matthieu-sgi/Internet-of-Plants/documentation/user_study/charts/plant_interaction_chart.png

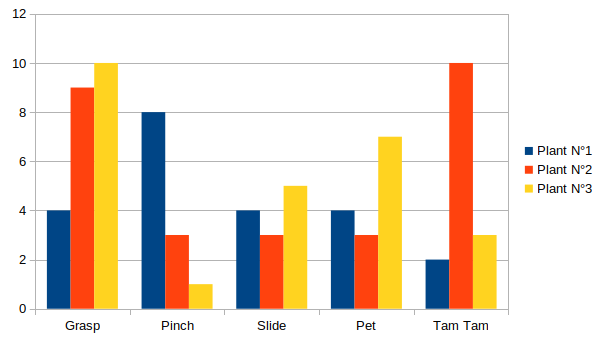
documentation/user_study/charts/plant_interaction_chart.png
