matthieu-sgi/Internet-of-Plants/documentation/user_study/media/IMG_20231115_154253.jpg

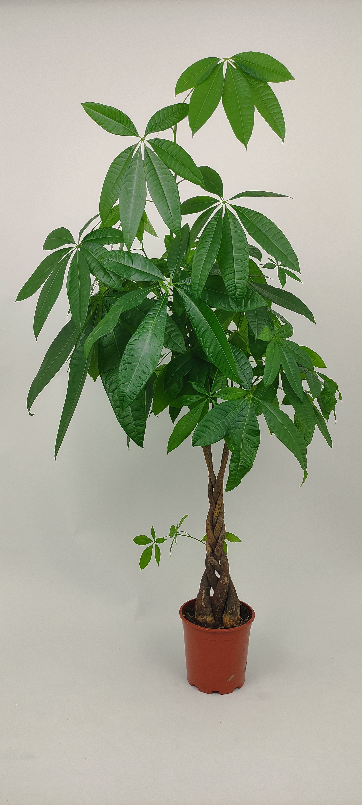
documentation/user_study/media/IMG_20231115_154253.jpg
