matthieu-sgi/Internet-of-Plants/documentation/user_study/media/IMG_20231115_154408.jpg

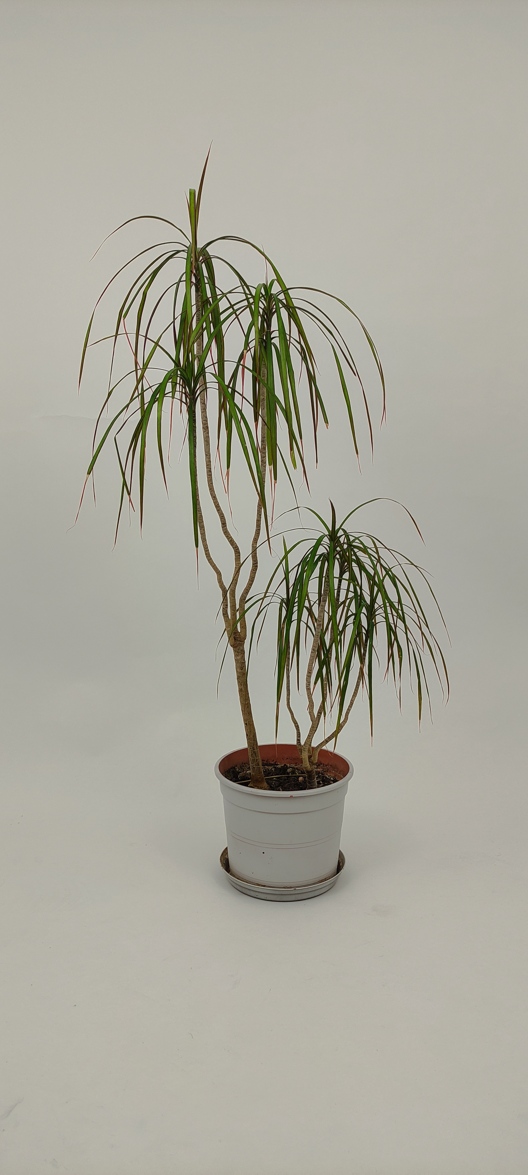
documentation/user_study/media/IMG_20231115_154408.jpg
