matthieu-sgi/Internet-of-Plants/documentation/user_study/media/IMG_20231115_155932.jpg

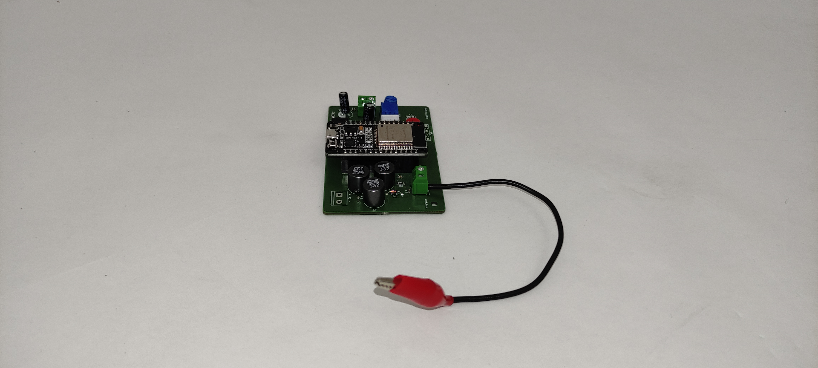
documentation/user_study/media/IMG_20231115_155932.jpg
