matthieu-sgi/Internet-of-Plants/documentation/user_study/media/IMG_20231115_160021.jpg

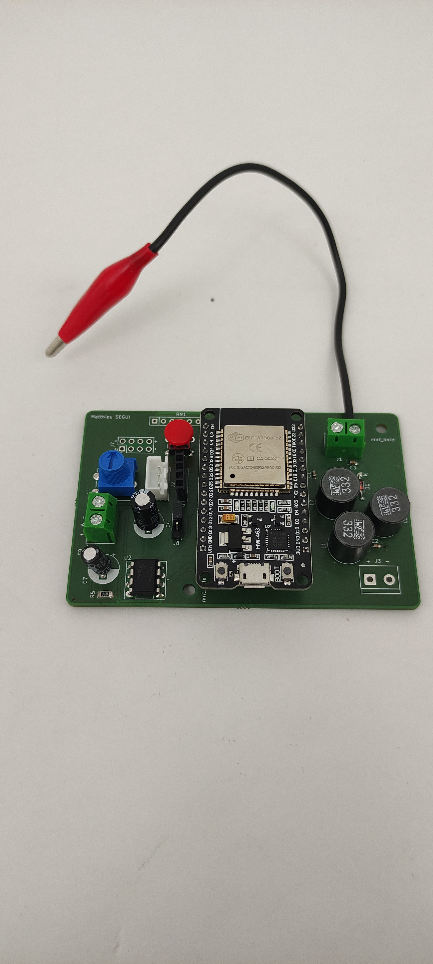
documentation/user_study/media/IMG_20231115_160021.jpg
