matthieu-sgi/Internet-of-Plants/documentation/user_study/media/raw/1699971025793.jpg

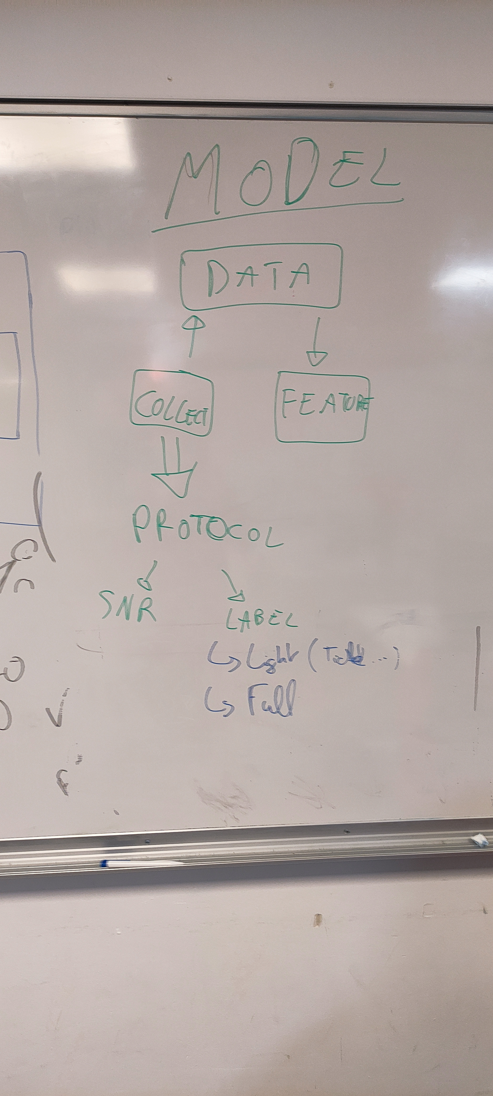
documentation/user_study/media/raw/1699971025793.jpg
