matthieu-sgi/Internet-of-Plants/documentation/user_study/media/raw/1699971025814.jpg

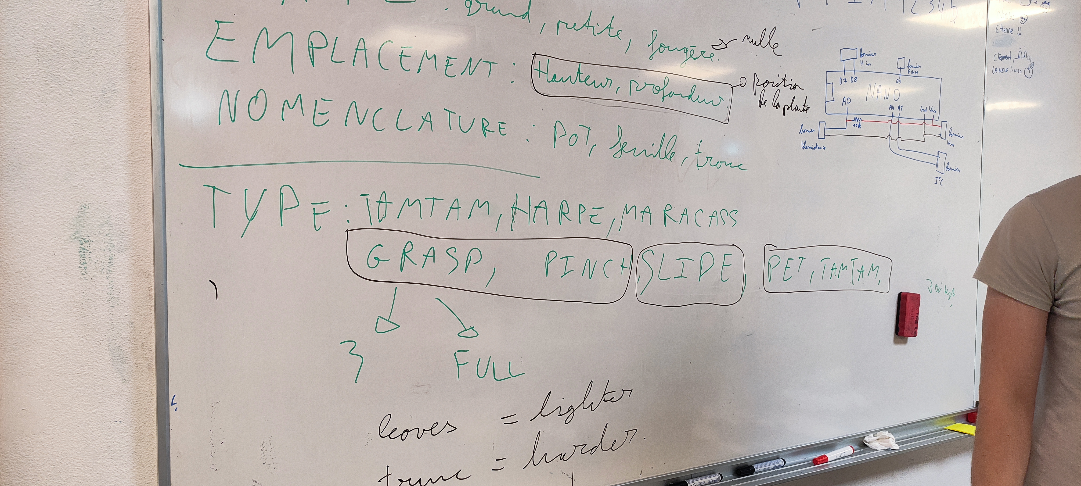
documentation/user_study/media/raw/1699971025814.jpg
