matthieu-sgi/Internet-of-Plants/documentation/user_study/user_study_plant_interaction/Images/iop_triangle.png

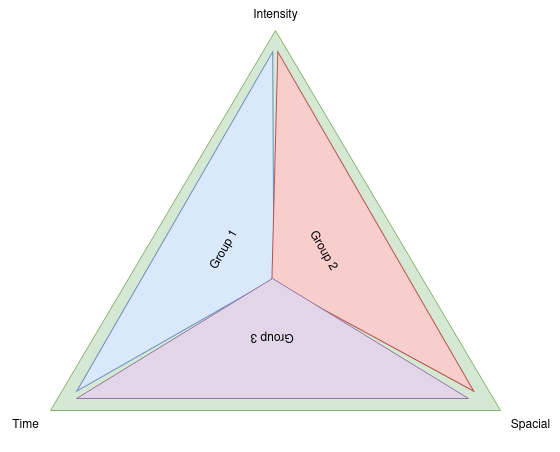
documentation/user_study/user_study_plant_interaction/Images/iop_triangle.png
