matthieu-sgi/Internet-of-Plants/media/3D_view_front.png

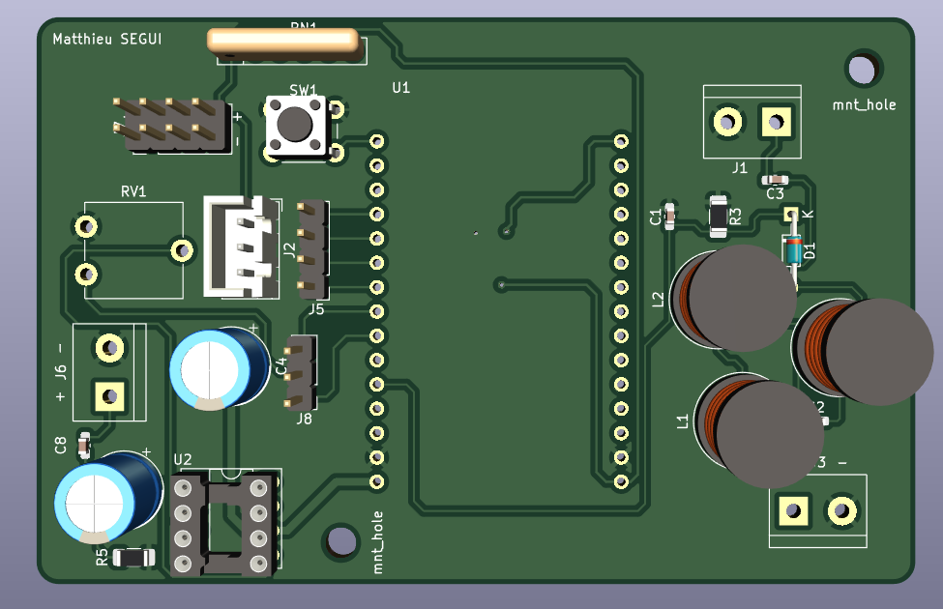
media/3D_view_front.png
