matthieu-sgi/Internet-of-Plants/media/3D_view_front_modif.png

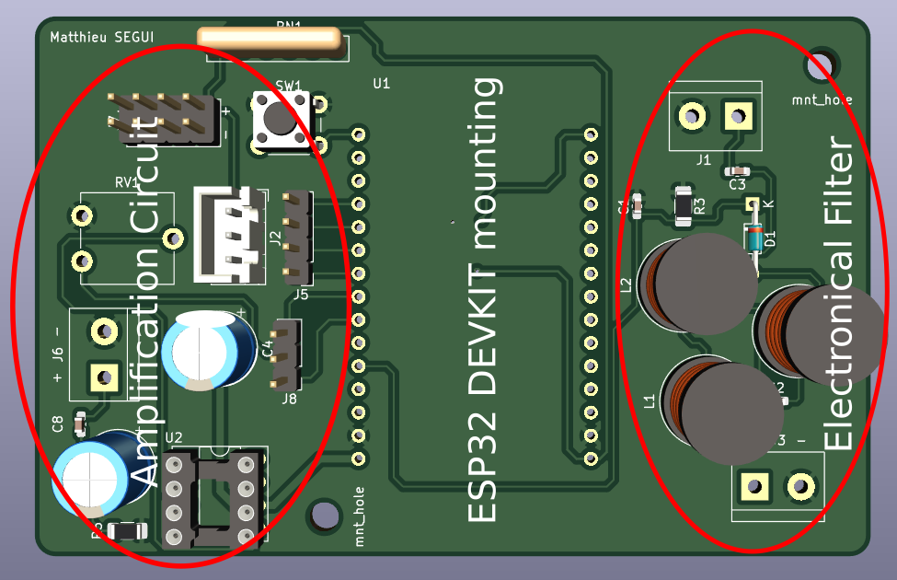
media/3D_view_front_modif.png
