matthieu-sgi/Internet-of-Plants/media/esp32_signal.jpg

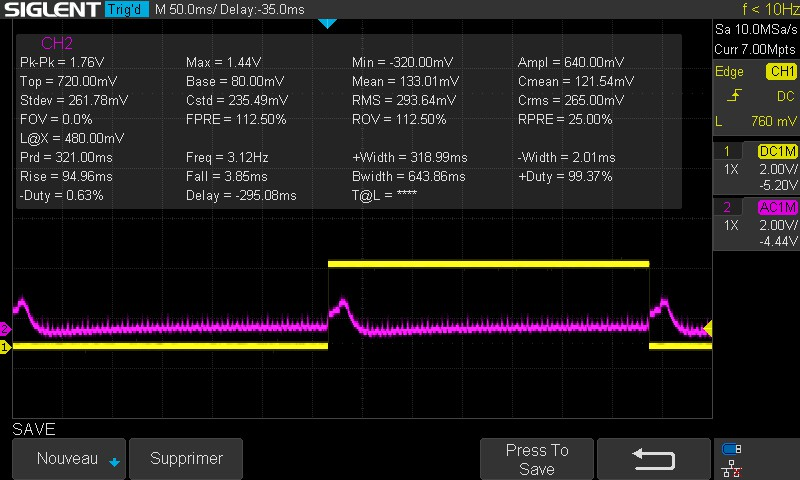
media/esp32_signal.jpg
