matthieu-sgi/Internet-of-Plants/media/pd_patch.png

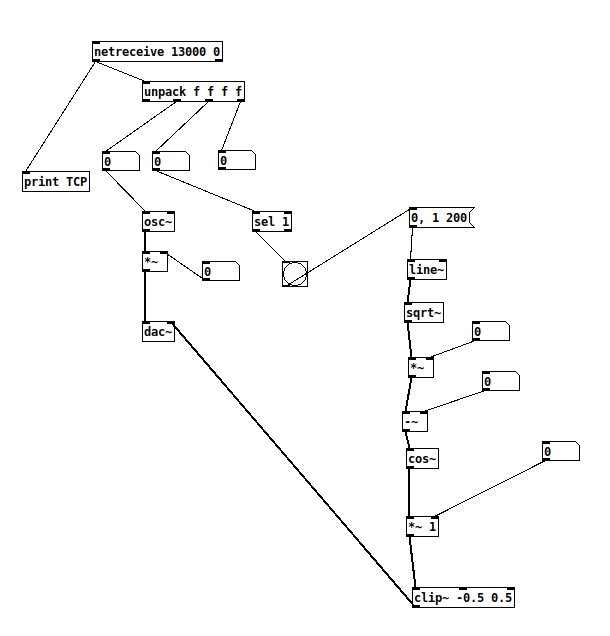
media/pd_patch.png
