matthieu-sgi/Internet-of-Plants/software/server/diagram/iop_uml_diagram.png

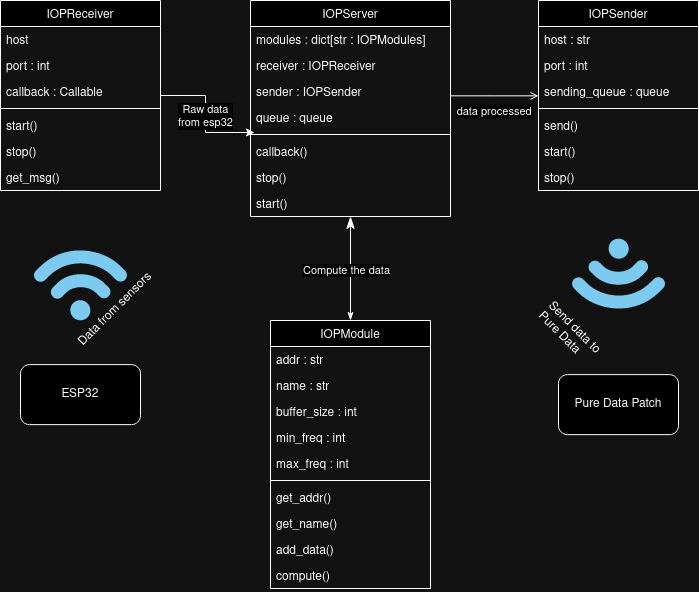
software/server/diagram/iop_uml_diagram.png
