matthieu-sgi/Internet-of-Plants/software/.other/tests/synthetizer/include/sound_hex.h

u_int8_t sound_wav[] = {
  0xd4, 0xfd, 0xd6, 0xfc, 0x64, 0xfc, 0x7d, 0xfe, 0x83, 0xfc, 0x99, 0x01,
  0x38, 0xfe, 0xea, 0x01, 0x7d, 0xfe, 0x9f, 0x01, 0x1d, 0xff, 0x4e, 0x02,
  0x72, 0x01, 0x48, 0x02, 0x7d, 0x02, 0x1c, 0x02, 0x15, 0x02, 0x97, 0x01,
  0x84, 0x01, 0xd6, 0x01, 0x3b, 0x02, 0xd0, 0x02, 0x66, 0x04, 0x2d, 0x02,
  0xed, 0x04, 0xf1, 0xff, 0x03, 0x04, 0x10, 0x00, 0x55, 0x03, 0xab, 0x01,
  0x07, 0x02, 0xce, 0x00, 0xf5, 0xff, 0x4f, 0xff, 0x05, 0xff, 0xc0, 0xfe,
  0xbd, 0xff, 0x8f, 0xfe, 0xf5, 0xff, 0x9e, 0xfd, 0x26, 0xfd, 0x56, 0xfb,
  0xc3, 0xfa, 0x3a, 0xfa, 0x8a, 0xfa, 0x7f, 0xf9, 0x98, 0xfa, 0xdd, 0xf7,
  0x1a, 0xfa, 0x21, 0xf8, 0xc1, 0xf9, 0xee, 0xfa, 0xe5, 0xfa, 0x9d, 0xfd,
  0x4d, 0xfc, 0xe8, 0xfe, 0x9d, 0xfc, 0x68, 0x00, 0xc8, 0xfd, 0x45, 0x02,
  0xc1, 0xff, 0x26, 0x03, 0xf4, 0x00, 0x71, 0x03, 0x13, 0x02, 0xd4, 0x03,
  0x55, 0x02, 0x8f, 0x04, 0xaa, 0x03, 0x41, 0x04, 0x98, 0x05, 0x18, 0x02,
  0xff, 0x05, 0x80, 0x00, 0x1c, 0x05, 0xf9, 0x00, 0x43, 0x04, 0x4b, 0x00,
  0xad, 0x03, 0x70, 0xfe, 0x47, 0x03, 0x92, 0xfe, 0x8a, 0x03, 0x7e, 0x00,
  0x1a, 0x04, 0x00, 0x02, 0xa1, 0x03, 0xe4, 0x01, 0x65, 0x00, 0xc1, 0x00,
  0xda, 0xfc, 0x98, 0x00, 0x3e, 0xfb, 0xcb, 0xff, 0x72, 0xfa, 0x96, 0xfd,
  0x45, 0xf9, 0xf2, 0xfc, 0xcf, 0xf8, 0xe6, 0xfe, 0x5f, 0xfa, 0x10, 0x01,
  0x43, 0xfc, 0xe2, 0x01, 0xbb, 0xfd, 0x2f, 0x03, 0x50, 0x00, 0x80, 0x04,
  0xe6, 0x02, 0x23, 0x04, 0xbe, 0x03, 0x62, 0x03, 0x48, 0x03, 0xcf, 0x03,
  0xc3, 0x03, 0x6f, 0x04, 0xb9, 0x05, 0x1a, 0x03, 0xfd, 0x06, 0x54, 0x00,
  0x62, 0x06, 0x48, 0xff, 0xab, 0x04, 0x2e, 0xff, 0x2a, 0x03, 0x01, 0xfe,
  0x17, 0x01, 0x49, 0xfc, 0xe1, 0xfe, 0x2b, 0xfc, 0x87, 0xfe, 0xe6, 0xfc,
  0x93, 0xff, 0xbb, 0xfc, 0x55, 0xff, 0x71, 0xfc, 0xa9, 0xfc, 0x2a, 0xfd,
  0x4d, 0xfa, 0x8c, 0xfe, 0x42, 0xf9, 0x09, 0xfe, 0x95, 0xf8, 0x35, 0xfc,
  0x6a, 0xf8, 0x5b, 0xfc, 0x8a, 0xf8, 0x56, 0xfe, 0x4c, 0xf9, 0xfe, 0xfe,
  0x60, 0xfa, 0x41, 0xfe, 0x9d, 0xfc, 0x85, 0xfe, 0x3c, 0x00, 0x80, 0xff,
  0xc9, 0x02, 0x74, 0xff, 0x3e, 0x03, 0xb0, 0xff, 0xa1, 0x03, 0x81, 0x01,
  0x92, 0x05, 0xb1, 0x02, 0xad, 0x06, 0xae, 0x01, 0x34, 0x06, 0x19, 0x01,
  0xf7, 0x05, 0x00, 0x02, 0x2c, 0x05, 0x71, 0x02, 0x93, 0x03, 0xa0, 0x01,
  0xd2, 0x01, 0x84, 0x00, 0x54, 0x01, 0xb5, 0x01, 0x0d, 0x02, 0x80, 0x02,
  0x5f, 0x01, 0xdc, 0x00, 0xfc, 0xff, 0x86, 0xff, 0x94, 0xfe, 0x0c, 0x00,
  0xe0, 0xfc, 0x34, 0x01, 0xd1, 0xfb, 0x55, 0x00, 0xa4, 0xfb, 0xb2, 0xfe,
  0xe1, 0xfb, 0x9b, 0xff, 0x19, 0xfc, 0xbd, 0x01, 0x56, 0xfc, 0x6e, 0x02,
  0xdd, 0xfc, 0xca, 0x01, 0x94, 0xfe, 0xb8, 0x01, 0x27, 0x00, 0xe5, 0x01,
  0xed, 0x00, 0x56, 0x00, 0x51, 0x01, 0x8f, 0xff, 0x8a, 0x02, 0x6a, 0x00,
  0x85, 0x04, 0x13, 0x01, 0x7a, 0x05, 0xb5, 0x00, 0x14, 0x06, 0xc7, 0xff,
  0x6d, 0x06, 0xcc, 0xff, 0xc4, 0x04, 0x35, 0x01, 0x2c, 0x02, 0xde, 0x00,
  0x02, 0x00, 0xc1, 0x00, 0x84, 0xff, 0xdb, 0x02, 0x6b, 0xff, 0x7e, 0x02,
  0x7c, 0xfe, 0xf2, 0xff, 0x17, 0xfe, 0x28, 0xfe, 0x4f, 0xfd, 0xbd, 0xfd,
  0x6a, 0xfb, 0xa7, 0xfc, 0x26, 0xf9, 0x80, 0xf9, 0x6c, 0xf8, 0x2c, 0xf7,
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

};
